azhn/smartbike/software/drivers/ServoControl.h

#ifndef SERVOCONTROL_H_
#define SERVOCONTROL_H_

#include <stdbool.h>
#include <stdint.h>

#include "pwm.h"
#include "BikeState.h"

#define REAR_PWM 0
#define FRONT_PWM 1
#define NUM_GEARS 6

void update_servos(State* state);

#endif // SERVOCONTROL_H_
