azhn/smartbike/software/apps/smartbike/our_service.c

/* Copyright (c) Nordic Semiconductor ASA
 * All rights reserved.
 * 
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
 *   3. Neither the name of Nordic Semiconductor ASA nor the names of other
 *   contributors to this software may be used to endorse or promote products
 *   derived from this software without specific prior written permission.
 * 
 *   4. This software must only be used in a processor manufactured by Nordic
 *   Semiconductor ASA, or in a processor manufactured by a third party that
 *   is used in combination with a processor manufactured by Nordic Semiconductor.
 * 
 * 
 * THIS SOFTWARE IS PROVIDED BY THE COPYRIGHT HOLDERS AND CONTRIBUTORS "AS IS" AND
 * ANY EXPRESS OR IMPLIED WARRANTIES, INCLUDING, BUT NOT LIMITED TO, THE IMPLIED
 * WARRANTIES OF MERCHANTABILITY AND FITNESS FOR A PARTICULAR PURPOSE ARE
 * DISCLAIMED. IN NO EVENT SHALL THE COPYRIGHT HOLDER OR CONTRIBUTORS BE LIABLE FOR
 * ANY DIRECT, INDIRECT, INCIDENTAL, SPECIAL, EXEMPLARY, OR CONSEQUENTIAL DAMAGES
 * (INCLUDING, BUT NOT LIMITED TO, PROCUREMENT OF SUBSTITUTE GOODS OR SERVICES;
 * LOSS OF USE, DATA, OR PROFITS; OR BUSINESS INTERRUPTION) HOWEVER CAUSED AND ON
 * ANY THEORY OF LIABILITY, WHETHER IN CONTRACT, STRICT LIABILITY, OR TORT
 * (INCLUDING NEGLIGENCE OR OTHERWISE) ARISING IN ANY WAY OUT OF THE USE OF THIS
 * SOFTWARE, EVEN IF ADVISED OF THE POSSIBILITY OF SUCH DAMAGE.
 * 
 */

#include <stdint.h>
#include <string.h>
#include "our_service.h"
#include "ble_srv_common.h"
#include "app_error.h"
//#include "SEGGER_RTT.h"

/**@brief Function for initiating our new service.
 *
 * @param[in]   p_our_service        Our Service structure.
 *
 */
void our_service_init(ble_os_t * p_our_service)
{
    uint32_t   err_code; // Variable to hold return codes from library and softdevice functions
    
    // OUR_JOB: Declare 16 bit service and 128 bit base UUIDs and add them to BLE stack table     
    ble_uuid_t                  service_uuid;
    ble_uuid128_t base_uuid     = BLE_UUID_OUR_BASE_UUID;
    service_uuid.uuid           = BLE_UUID_OUR_SERVICE;
    err_code                    = sd_ble_uuid_vs_add(&base_uuid, &service_uuid.type);
    APP_ERROR_CHECK(err_code);

    // OUR_JOB: Add our service
    err_code                    = sd_ble_gatts_service_add(BLE_GATTS_SRVC_TYPE_PRIMARY,
                                                               &service_uuid,
                                                               &p_our_service->service_handle);
    APP_ERROR_CHECK(err_code);   


    // Print messages to Segger Real Time Terminal
    // UNCOMMENT THE FOUR LINES BELOW AFTER INITIALIZING THE SERVICE OR THE EXAMPLE WILL NOT COMPILE.
//    SEGGER_RTT_WriteString(0, "Exectuing our_service_init().\n"); // Print message to RTT to the application flow
//    SEGGER_RTT_printf(0, "Service UUID: 0x%#04x\n", service_uuid.uuid); // Print service UUID should match definition BLE_UUID_OUR_SERVICE
//    SEGGER_RTT_printf(0, "Service UUID type: 0x%#02x\n", service_uuid.type); // Print UUID type. Should match BLE_UUID_TYPE_VENDOR_BEGIN. Search for BLE_UUID_TYPES in ble_types.h for more info
//    SEGGER_RTT_printf(0, "Service handle: 0x%#04x\n", p_our_service->service_handle); // Print out the service handle. Should match service handle shown in MCP under Attribute values
}
